jonatso/GuitarZero/mcu/src/crockett.h

#include "mini_midi.h"
#include <stdbool.h>

// Notes
note_t crocetts_theme_note0 = {
  110,
  1,
  50,
  0,
  false
};
note_t crocetts_theme_note1 = {
  117,
  1,
  38,
  0,
  false
};
note_t crocetts_theme_note2 = {
  112,
  1,
  38,
  0,
  false
};
note_t crocetts_theme_note3 = {
  119,
  1,
  50,
  0,
  false
};
note_t crocetts_theme_note4 = {
  110,
  1,
  38,
  0,
  false
};
note_t crocetts_theme_note5 = {
  104,
  1,
  50,
  0,
  false
};
note_t crocetts_theme_note6 = {
  115,
  1,
  38,
  0,
  false
};
note_t crocetts_theme_note7 = {
  107,
  1,
  38,
  0,
  false
};
note_t crocetts_theme_note8 = {
  122,
  1,
  38,
  0,
  false
};
note_t crocetts_theme_note9 = {
  119,
  1,
  38,
  0,
  false
};
note_t crocetts_theme_note10 = {
  108,
  1,
  38,
  0,
  false
};
note_t crocetts_theme_note11 = {
  116,
  1,
  38,
  0,
  false
};
note_t crocetts_theme_note12 = {
  105,
  1,
  50,
  0,
  false
};
note_t crocetts_theme_note13 = {
  103,
  1,
  50,
  0,
  false
};
note_t crocetts_theme_note14 = {
  121,
  1,
  50,
  0,
  false
};
note_t crocetts_theme_note15 = {
  117,
  1,
  50,
  0,
  false
};
note_t crocetts_theme_note16 = {
  105,
  1,
  38,
  0,
  false
};
note_t crocetts_theme_note17 = {
  112,
  1,
  50,
  0,
  false
};
note_t crocetts_theme_note18 = {
  109,
  1,
  50,
  0,
  false
};
note_t crocetts_theme_note19 = {
  116,
  1,
  50,
  0,
  false
};
note_t crocetts_theme_note20 = {
  122,
  1,
  50,
  0,
  false
};
note_t crocetts_theme_note21 = {
  105,
  1,
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
  0,
  72,
  3,
  false
};
note_t crocetts_theme_note468 = {
  101,
  0,
  67,
  3,
  false
};
note_t crocetts_theme_note469 = {
  100,
  0,
  68,
  4,
  false
};
note_t crocetts_theme_note470 = {
  95,
  0,
  69,
  5,
  false
};
note_t crocetts_theme_note471 = {
  95,
  0,
  62,
  3,
  false
};
note_t* crocetts_theme_unique_notes[] = {&crocetts_theme_note0,&crocetts_theme_note1,&crocetts_theme_note2,&crocetts_theme_note3,&crocetts_theme_note4,&crocetts_theme_note5,&crocetts_theme_note6,&crocetts_theme_note7,&crocetts_theme_note8,&crocetts_theme_note9,&crocetts_theme_note10,&crocetts_theme_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
};
sixteenth_t crocetts_theme_sixteenth869 = {
  6,
  (uint16_t[]){162,256,187,183,306,320}
};
sixteenth_t crocetts_theme_sixteenth870 = {
  7,
  (uint16_t[]){93,256,187,183,306,378,467}
};
sixteenth_t crocetts_theme_sixteenth871 = {
  6,
  (uint16_t[]){93,256,187,183,306,378}
};
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
