jonatso/GuitarZero/mcu/src/supermario.h

#include "mini_midi.h"
#include <stdbool.h>

// Notes
note_t super_mario_note0 = {
  67,
  0,
  76,
  2,
  false
};
note_t super_mario_note1 = {
  67,
  0,
  72,
  3,
  false
};
note_t super_mario_note2 = {
  67,
  0,
  79,
  5,
  false
};
note_t super_mario_note3 = {
  67,
  0,
  67,
  3,
  false
};
note_t super_mario_note4 = {
  67,
  0,
  64,
  5,
  false
};
note_t super_mario_note5 = {
  67,
  0,
  69,
  5,
  false
};
note_t super_mario_note6 = {
  67,
  0,
  71,
  2,
  false
};
note_t super_mario_note7 = {
  67,
  0,
  70,
  1,
  false
};
note_t super_mario_note8 = {
  67,
  0,
  81,
  2,
  false
};
note_t super_mario_note9 = {
  67,
  0,
  77,
  3,
  false
};
note_t super_mario_note10 = {
  67,
  0,
  74,
  5,
  false
};
note_t super_mario_note11 = {
  67,
  0,
  78,
  4,
  false
};
note_t super_mario_note12 = {
  67,
  0,
  75,
  1,
  false
};
note_t super_mario_note13 = {
  67,
  0,
  68,
  4,
  false
};
note_t super_mario_note14 = {
  67,
  0,
  84,
  5,
  false
};
note_t super_mario_note15 = {
  67,
  4,
  76,
  0,
  true
};
note_t super_mario_note16 = {
  67,
  4,
  72,
  0,
  true
};
note_t super_mario_note17 = {
  67,
  4,
  79,
  0,
  true
};
note_t super_mario_note18 = {
  67,
  4,
  67,
  0,
  true
};
note_t super_mario_note19 = {
  67,
  4,
  64,
  0,
  true
};
note_t super_mario_note20 = {
  67,
  4,
  69,
  0,
  true
};
note_t super_mario_note21 = {
  67,
  4,
  71,
  0,
  true
};
note_t super_mario_note22 = {
  67,
  4,
  70,
  0,
  true
};
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
th117,&super_mario_sixteenth118};
// Song
uint16_t super_mario_sixteenth_indexes[] = {0,0,1,0,1,2,3,1,4,1,1,1,5,1,1,1,6,1,1,7,1,1,8,1,1,9,1,10,1,11,12,1,13,14,1,15,16,1,17,18,1,19,1,20,21,22,1,1,23,1,1,24,1,1,25,1,1,26,1,22,1,27,26,1,24,28,1,29,30,1,31,32,1,33,1,34,21,22,1,1,35,1,36,37,38,39,40,41,42,43,44,45,40,46,47,48,35,1,49,50,51,52,53,54,1,55,1,55,55,1,53,1,35,1,56,57,58,59,40,60,42,61,62,63,40,64,65,66,35,1,67,1,1,68,1,1,69,1,1,53,53,1,35,1,35,1,56,57,58,59,40,60,42,61,62,63,40,64,65,66,35,1,56,70,58,59,53,71,1,55,1,55,55,1,53,1,35,1,56,57,58,59,40,60,42,61,62,63,40,64,65,66,35,1,67,1,1,68,1,1,69,1,1,53,53,1,35,1,72,73,1,74,1,73,75,1,76,77,1,78,79,1,80,1,72,73,1,74,1,73,75,81,53,1,1,35,1,1,80,1,72,73,1,74,1,73,75,1,76,77,1,78,79,1,80,1,82,82,1,82,1,83,82,1,84,1,1,1,85,1,1,1,86,1,1,87,1,1,88,1,1,89,1,90,1,91,89,1,87,92,1,93,94,1,95,96,1,97,1,98,99,90,1,1,86,1,1,87,1,1,88,1,1,89,1,90,1,91,89,1,87,92,1,93,94,1,95,96,1,97,1,98,99,90,1,1,100,101,1,102,53,1,103,1,104,105,42,105,106,40,42,1,107,108,1,109,110,56,111,93,112,101,53,62,113,40,53,1,100,101,1,102,53,1,103,1,104,105,42,105,106,40,42,1,114,115,1,115,115,116,1,93,63,117,53,117,118,1,1,1,100,101,1,102,53,1,103,1,104,105,42,105,106,40,42,1,107,108,1,109,110,56,111,93,112,101,53,62,113,40,53,1,100,101,1,102,53,1,103,1,104,105,42,105,106,40,42,1,114,115,1,115,115,116,1,93,63,117,53,117,118,1,1,1,72,73,1,74,1,73,75,1,76,77,1,78,79,1,80,1,72,73,1,74,1,73,75,81,53,1,1,35,1,1,80,1,72,73,1,74,1,73,75,1,76,77,1,78,79,1,80,1,82,82,1,82,1,83,82,1,84,1,1,1,85,1,1,1,100,101,1,102,53,1,103,1,104,105,42,105,106,40,42,1,107,108,1,109,110,56,111,93,112,101,53,62,113,40,53,1,100,101,1,102,53,1,103,1,104,105,42,105,106,40,42,1,114,115,1,115,115,116,1,93,63,117,53,117,118,1,1,1};
song_t super_mario_song = {
  "SUPER MARIO",
  90,
  37,
  119,
  66,
  super_mario_sixteenth_indexes,
  super_mario_unique_sixteenths,
  super_mario_unique_notes
};
