jonatso/GuitarZero/mcu/src/bjornen_sover.h

#include "mini_midi.h"
#include <stdbool.h>

// Notes
note_t bjornen_sover_note0 = {
  68,
  2,
  52,
  0,
  false
};
note_t bjornen_sover_note1 = {
  68,
  2,
  48,
  0,
  false
};
note_t bjornen_sover_note2 = {
  68,
  2,
  55,
  0,
  false
};
note_t bjornen_sover_note3 = {
  75,
  2,
  47,
  0,
  false
};
note_t bjornen_sover_note4 = {
  75,
  2,
  50,
  0,
  false
};
note_t bjornen_sover_note5 = {
  75,
  2,
  55,
  0,
  false
};
note_t bjornen_sover_note6 = {
  74,
  2,
  55,
  0,
  false
};
note_t bjornen_sover_note7 = {
  74,
  2,
  52,
  0,
  false
};
note_t bjornen_sover_note8 = {
  74,
  2,
  48,
  0,
  false
};
note_t bjornen_sover_note9 = {
  77,
  2,
  47,
  0,
  false
};
note_t bjornen_sover_note10 = {
  77,
  2,
  50,
  0,
  false
};
note_t bjornen_sover_note11 = {
  77,
  2,
  55,
  0,
  false
};
note_t bjornen_sover_note12 = {
  76,
  2,
  55,
  0,
  false
};
note_t bjornen_sover_note13 = {
  76,
  2,
  52,
  0,
  false
};
note_t bjornen_sover_note14 = {
  76,
  2,
  48,
  0,
  false
};
note_t bjornen_sover_note15 = {
  72,
  2,
  55,
  0,
  false
};
note_t bjornen_sover_note16 = {
  72,
  2,
  52,
  0,
  false
};
note_t bjornen_sover_note17 = {
  72,
  2,
  48,
  0,
  false
};
note_t bjornen_sover_note18 = {
  92,
  2,
  55,
  0,
  false
};
note_t bjornen_sover_note19 = {
  92,
  2,
  50,
  0,
  false
};
note_t bjornen_sover_note20 = {
  92,
  2,
  47,
  0,
  false
};
note_t bjornen_sover_note21 = {
  79,
  2,
  48,
  0,
  false
};
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
  5,
  (uint16_t[]){11,9,10,45,73}
};
sixteenth_t bjornen_sover_sixteenth71 = {
  4,
  (uint16_t[]){11,9,10,45}
};
sixteenth_t bjornen_sover_sixteenth72 = {
  5,
  (uint16_t[]){15,16,17,24,73}
};
sixteenth_t bjornen_sover_sixteenth73 = {
  4,
  (uint16_t[]){15,16,17,24}
};
sixteenth_t* bjornen_sover_unique_sixteenths[] = {&bjornen_sover_sixteenth0,&bjornen_sover_sixteenth1,&bjornen_sover_sixteenth2,&bjornen_sover_sixteenth3,&bjornen_sover_sixteenth4,&bjornen_sover_sixteenth5,&bjornen_sover_sixteenth6,&bjornen_sover_sixteenth7,&bjornen_sover_sixteenth8,&bjornen_sover_sixteenth9,&bjornen_sover_sixteenth10,&bjornen_sover_sixteenth11,&bjornen_sover_sixteenth12,&bjornen_sover_sixteenth13,&bjornen_sover_sixteenth14,&bjornen_sover_sixteenth15,&bjornen_sover_sixteenth16,&bjornen_sover_sixteenth17,&bjornen_sover_sixteenth18,&bjornen_sover_sixteenth19,&bjornen_sover_sixteenth20,&bjornen_sover_sixteenth21,&bjornen_sover_sixteenth22,&bjornen_sover_sixteenth23,&bjornen_sover_sixteenth24,&bjornen_sover_sixteenth25,&bjornen_sover_sixteenth26,&bjornen_sover_sixteenth27,&bjornen_sover_sixteenth28,&bjornen_sover_sixteenth29,&bjornen_sover_sixteenth30,&bjornen_sover_sixteenth31,&bjornen_sover_sixteenth32,&bjornen_sover_sixteenth33,&bjornen_sover_sixteenth34,&bjornen_sover_sixteenth35,&bjornen_sover_sixteenth36,&bjornen_sover_sixteenth37,&bjornen_sover_sixteenth38,&bjornen_sover_sixteenth39,&bjornen_sover_sixteenth40,&bjornen_sover_sixteenth41,&bjornen_sover_sixteenth42,&bjornen_sover_sixteenth43,&bjornen_sover_sixteenth44,&bjornen_sover_sixteenth45,&bjornen_sover_sixteenth46,&bjornen_sover_sixteenth47,&bjornen_sover_sixteenth48,&bjornen_sover_sixteenth49,&bjornen_sover_sixteenth50,&bjornen_sover_sixteenth51,&bjornen_sover_sixteenth52,&bjornen_sover_sixteenth53,&bjornen_sover_sixteenth54,&bjornen_sover_sixteenth55,&bjornen_sover_sixteenth56,&bjornen_sover_sixteenth57,&bjornen_sover_sixteenth58,&bjornen_sover_sixteenth59,&bjornen_sover_sixteenth60,&bjornen_sover_sixteenth61,&bjornen_sover_sixteenth62,&bjornen_sover_sixteenth63,&bjornen_sover_sixteenth64,&bjornen_sover_sixteenth65,&bjornen_sover_sixteenth66,&bjornen_sover_sixteenth67,&bjornen_sover_sixteenth68,&bjornen_sover_sixteenth69,&bjornen_sover_sixteenth70,&bjornen_sover_sixteenth71,&bjornen_sover_sixteenth72,&bjornen_sover_sixteenth73};
// Song
uint16_t bjornen_sover_sixteenth_indexes[] = {0,1,1,1,2,3,3,3,4,5,5,5,6,7,7,7,8,9,9,9,10,11,11,11,12,13,13,13,14,15,15,15,16,17,17,17,16,17,17,17,18,19,19,19,20,21,21,21,22,23,23,23,23,23,23,23,23,23,23,23,23,23,23,23,24,25,25,25,26,27,27,27,28,29,29,29,30,31,31,31,32,33,33,33,33,33,33,33,34,35,35,35,35,35,35,35,36,37,37,37,38,39,39,39,40,41,41,41,42,43,43,43,44,45,45,45,45,45,45,45,46,47,47,47,47,47,47,47,48,49,49,49,50,51,51,51,52,53,53,53,54,55,55,55,56,57,57,57,58,59,59,59,60,61,61,61,62,63,63,63,64,65,65,65,66,67,67,67,68,69,69,69,70,71,71,71,72,73,73,73,73,73,73,73,73,73,73,73,73,73,73,73};
song_t bjornen_sover_song = {
  "BJORNEN SOVER",
  100,
  12,
  74,
  74,
  bjornen_sover_sixteenth_indexes,
  bjornen_sover_unique_sixteenths,
  bjornen_sover_unique_notes
};
