jonatso/GuitarZero/mcu/src/eye_of_the_tiger.h

#include "mini_midi.h"
#include <stdbool.h>

// Notes
note_t eye_of_the_tiger_note0 = {
  117,
  4,
  65,
  0,
  true
};
note_t eye_of_the_tiger_note1 = {
  117,
  4,
  77,
  0,
  true
};
note_t eye_of_the_tiger_note2 = {
  112,
  4,
  68,
  0,
  true
};
note_t eye_of_the_tiger_note3 = {
  112,
  4,
  80,
  0,
  true
};
note_t eye_of_the_tiger_note4 = {
  114,
  4,
  65,
  0,
  true
};
note_t eye_of_the_tiger_note5 = {
  114,
  4,
  77,
  0,
  true
};
note_t eye_of_the_tiger_note6 = {
  121,
  4,
  63,
  0,
  true
};
note_t eye_of_the_tiger_note7 = {
  121,
  4,
  75,
  0,
  true
};
note_t eye_of_the_tiger_note8 = {
  94,
  4,
  61,
  0,
  true
};
note_t eye_of_the_tiger_note9 = {
  94,
  4,
  73,
  0,
  true
};
note_t eye_of_the_tiger_note10 = {
  96,
  4,
  65,
  0,
  true
};
note_t eye_of_the_tiger_note11 = {
  96,
  4,
  77,
  0,
  true
};
note_t eye_of_the_tiger_note12 = {
  95,
  4,
  75,
  0,
  true
};
note_t eye_of_the_tiger_note13 = {
  95,
  4,
  63,
  0,
  true
};
note_t eye_of_the_tiger_note14 = {
  101,
  4,
  73,
  0,
  true
};
note_t eye_of_the_tiger_note15 = {
  101,
  4,
  61,
  0,
  true
};
note_t eye_of_the_tiger_note16 = {
  91,
  4,
  73,
  0,
  true
};
note_t eye_of_the_tiger_note17 = {
  91,
  4,
  61,
  0,
  true
};
note_t eye_of_the_tiger_note18 = {
  94,
  4,
  63,
  0,
  true
};
note_t eye_of_the_tiger_note19 = {
  94,
  4,
  75,
  0,
  true
};
note_t eye_of_the_tiger_note20 = {
  93,
  4,
  75,
  0,
  true
};
note_t eye_of_the_tiger_note21 = {
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
e_of_the_tiger_note464,&eye_of_the_tiger_note465,&eye_of_the_tiger_note466,&eye_of_the_tiger_note467,&eye_of_the_tiger_note468,&eye_of_the_tiger_note469,&eye_of_the_tiger_note470,&eye_of_the_tiger_note471,&eye_of_the_tiger_note472,&eye_of_the_tiger_note473,&eye_of_the_tiger_note474,&eye_of_the_tiger_note475,&eye_of_the_tiger_note476,&eye_of_the_tiger_note477,&eye_of_the_tiger_note478,&eye_of_the_tiger_note479,&eye_of_the_tiger_note480,&eye_of_the_tiger_note481,&eye_of_the_tiger_note482,&eye_of_the_tiger_note483,&eye_of_the_tiger_note484,&eye_of_the_tiger_note485,&eye_of_the_tiger_note486,&eye_of_the_tiger_note487,&eye_of_the_tiger_note488,&eye_of_the_tiger_note489,&eye_of_the_tiger_note490,&eye_of_the_tiger_note491,&eye_of_the_tiger_note492,&eye_of_the_tiger_note493,&eye_of_the_tiger_note494,&eye_of_the_tiger_note495,&eye_of_the_tiger_note496,&eye_of_the_tiger_note497,&eye_of_the_tiger_note498,&eye_of_the_tiger_note499,&eye_of_the_tiger_note500,&eye_of_the_tiger_note501,&eye_of_the_tiger_note502,&eye_of_the_tiger_note503,&eye_of_the_tiger_note504,&eye_of_the_tiger_note505,&eye_of_the_tiger_note506,&eye_of_the_tiger_note507,&eye_of_the_tiger_note508,&eye_of_the_tiger_note509,&eye_of_the_tiger_note510,&eye_of_the_tiger_note511,&eye_of_the_tiger_note512,&eye_of_the_tiger_note513,&eye_of_the_tiger_note514,&eye_of_the_tiger_note515,&eye_of_the_tiger_note516,&eye_of_the_tiger_note517,&eye_of_the_tiger_note518,&eye_of_the_tiger_note519,&eye_of_the_tiger_note520,&eye_of_the_tiger_note521,&eye_of_the_tiger_note522,&eye_of_the_tiger_note523,&eye_of_the_tiger_note524,&eye_of_the_tiger_note525,&eye_of_the_tiger_note526,&eye_of_the_tiger_note527,&eye_of_the_tiger_note528,&eye_of_the_tiger_note529,&eye_of_the_tiger_note530,&eye_of_the_tiger_note531,&eye_of_the_tiger_note532,&eye_of_the_tiger_note533,&eye_of_the_tiger_note534,&eye_of_the_tiger_note535,&eye_of_the_tiger_note536,&eye_of_the_tiger_note537,&eye_of_the_tiger_note538,&eye_of_the_tiger_note539,&eye_of_the_tiger_note540,&eye_of_the_tiger_note541,&eye_of_the_tiger_note542,&eye_of_the_tiger_note543,&eye_of_the_tiger_note544,&eye_of_the_tiger_note545,&eye_of_the_tiger_note546,&eye_of_the_tiger_note547,&eye_of_the_tiger_note548,&eye_of_the_tiger_note549,&eye_of_the_tiger_note550,&eye_of_the_tiger_note551,&eye_of_the_tiger_note552,&eye_of_the_tiger_note553,&eye_of_the_tiger_note554};
// Sixteenths
sixteenth_t eye_of_the_tiger_sixteenth0 = {
  0,
  (uint16_t[]){}
};
sixteenth_t eye_of_the_tiger_sixteenth1 = {
  8,
  (uint16_t[]){261,278,279,305,307,306,412,411}
};
sixteenth_t eye_of_the_tiger_sixteenth2 = {
  4,
  (uint16_t[]){261,306,412,411}
};
sixteenth_t eye_of_the_tiger_sixteenth3 = {
  8,
  (uint16_t[]){261,279,279,305,309,308,414,413}
};
sixteenth_t eye_of_the_tiger_sixteenth4 = {
  3,
  (uint16_t[]){261,414,413}
};
sixteenth_t eye_of_the_tiger_sixteenth5 = {
  8,
  (uint16_t[]){262,280,281,311,312,310,415,416}
};
sixteenth_t eye_of_the_tiger_sixteenth6 = {
  2,
  (uint16_t[]){262,416}
};
sixteenth_t eye_of_the_tiger_sixteenth7 = {
  8,
  (uint16_t[]){261,281,281,314,313,315,413,417}
};
sixteenth_t eye_of_the_tiger_sixteenth8 = {
  3,
  (uint16_t[]){261,413,417}
};
sixteenth_t eye_of_the_tiger_sixteenth9 = {
  2,
  (uint16_t[]){413,417}
};
sixteenth_t eye_of_the_tiger_sixteenth10 = {
  8,
  (uint16_t[]){261,281,281,317,308,316,419,418}
};
sixteenth_t eye_of_the_tiger_sixteenth11 = {
  3,
  (uint16_t[]){261,419,418}
};
sixteenth_t eye_of_the_tiger_sixteenth12 = {
  8,
  (uint16_t[]){262,281,281,318,319,312,420,416}
};
sixteenth_t eye_of_the_tiger_sixteenth13 = {
  1,
  (uint16_t[]){262}
};
sixteenth_t eye_of_the_tiger_sixteenth14 = {
  8,
  (uint16_t[]){261,281,281,306,320,305,414,412}
};
sixteenth_t eye_of_the_tiger_sixteenth15 = {
  3,
  (uint16_t[]){261,414,412}
};
sixteenth_t eye_of_the_tiger_sixteenth16 = {
  2,
  (uint16_t[]){414,412}
};
sixteenth_t eye_of_the_tiger_sixteenth17 = {
  8,
  (uint16_t[]){261,281,281,321,316,322,421,412}
};
sixteenth_t eye_of_the_tiger_sixteenth18 = {
  6,
  (uint16_t[]){261,321,316,322,421,412}
};
sixteenth_t eye_of_the_tiger_sixteenth19 = {
  7,
  (uint16_t[]){263,282,283,323,324,422,423}
};
sixteenth_t eye_of_the_tiger_sixteenth20 = {
  3,
  (uint16_t[]){263,422,423}
};
sixteenth_t eye_of_the_tiger_sixteenth21 = {
  8,
  (uint16_t[]){264,284,285,326,308,325,424,425}
};
sixteenth_t eye_of_the_tiger_sixteenth22 = {
  6,
  (uint16_t[]){264,326,308,325,424,425}
};
sixteenth_t eye_of_the_tiger_sixteenth23 = {
  4,
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
};
sixteenth_t eye_of_the_tiger_sixteenth735 = {
  9,
  (uint16_t[]){12,13,254,265,373,380,341,458,472}
};
sixteenth_t eye_of_the_tiger_sixteenth736 = {
  6,
  (uint16_t[]){12,13,265,373,380,341}
};
sixteenth_t eye_of_the_tiger_sixteenth737 = {
  5,
  (uint16_t[]){17,16,265,524,525}
};
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
