jonatso/GuitarZero/mcu/src/kickstart_my_heart.h

#include "mini_midi.h"
#include <stdbool.h>

// Notes
note_t kickstart_my_heart_note0 = {
  95,
  3,
  48,
  0,
  false
};
note_t kickstart_my_heart_note1 = {
  95,
  3,
  53,
  0,
  false
};
note_t kickstart_my_heart_note2 = {
  95,
  3,
  41,
  0,
  false
};
note_t kickstart_my_heart_note3 = {
  95,
  3,
  54,
  0,
  false
};
note_t kickstart_my_heart_note4 = {
  95,
  3,
  49,
  0,
  false
};
note_t kickstart_my_heart_note5 = {
  95,
  3,
  42,
  0,
  false
};
note_t kickstart_my_heart_note6 = {
  95,
  3,
  55,
  0,
  false
};
note_t kickstart_my_heart_note7 = {
  95,
  3,
  50,
  0,
  false
};
note_t kickstart_my_heart_note8 = {
  95,
  3,
  43,
  0,
  false
};
note_t kickstart_my_heart_note9 = {
  95,
  3,
  46,
  0,
  false
};
note_t kickstart_my_heart_note10 = {
  70,
  3,
  43,
  0,
  false
};
note_t kickstart_my_heart_note11 = {
  95,
  3,
  45,
  0,
  false
};
note_t kickstart_my_heart_note12 = {
  95,
  3,
  47,
  0,
  false
};
note_t kickstart_my_heart_note13 = {
  95,
  3,
  64,
  0,
  false
};
note_t kickstart_my_heart_note14 = {
  95,
  3,
  60,
  0,
  false
};
note_t kickstart_my_heart_note15 = {
  95,
  3,
  65,
  0,
  false
};
note_t kickstart_my_heart_note16 = {
  70,
  3,
  64,
  0,
  false
};
note_t kickstart_my_heart_note17 = {
  95,
  3,
  38,
  0,
  false
};
note_t kickstart_my_heart_note18 = {
  95,
  3,
  40,
  0,
  false
};
note_t kickstart_my_heart_note19 = {
  95,
  3,
  58,
  0,
  false
};
note_t kickstart_my_heart_note20 = {
  95,
  3,
  39,
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
  1,
  false
};
note_t kickstart_my_heart_note81 = {
  95,
  0,
  38,
  4,
  false
};
note_t kickstart_my_heart_note82 = {
  95,
  0,
  40,
  1,
  false
};
note_t kickstart_my_heart_note83 = {
  95,
  0,
  39,
  5,
  false
};
note_t kickstart_my_heart_note84 = {
  63,
  0,
  60,
  1,
  false
};
note_t kickstart_my_heart_note85 = {
  63,
  0,
  65,
  1,
  false
};
note_t kickstart_my_heart_note86 = {
  63,
  0,
  48,
  4,
  false
};
note_t kickstart_my_heart_note87 = {
  63,
  0,
  55,
  1,
  false
};
note_t kickstart_my_heart_note88 = {
  37,
  0,
  64,
  5,
  false
};
note_t kickstart_my_heart_note89 = {
  63,
  0,
  64,
  5,
  false
};
note_t kickstart_my_heart_note90 = {
  95,
  0,
  59,
  5,
  false
};
note_t kickstart_my_heart_note91 = {
  70,
  0,
  46,
  2,
  false
};
note_t kickstart_my_heart_note92 = {
  70,
  0,
  47,
  3,
  false
};
note_t kickstart_my_heart_note93 = {
  95,
  0,
  54,
  5,
  false
};
note_t kickstart_my_heart_note94 = {
  95,
  0,
  52,
  3,
  false
};
note_t kickstart_my_heart_note95 = {
  95,
  0,
  57,
  3,
  false
};
note_t* kickstart_my_heart_unique_notes[] = {&kickstart_my_heart_note0,&kickstart_my_heart_note1,&kickstart_my_heart_note2,&kickstart_my_heart_note3,&kickstart_my_heart_note4,&kickstart_my_heart_note5,&kickstart_my_heart_note6,&kickstart_my_heart_note7,&kickstart_my_heart_note8,&kickstart_my_heart_note9,&kickstart_my_heart_note10,&kickstart_my_heart_note11,&kickstart_my_heart_note12,&kickstart_my_heart_note13,&kickstart_my_heart_note14,&kickstart_my_heart_note15,&kickstart_my_heart_note16,&kickstart_my_heart_note17,&kickstart_my_heart_note18,&kickstart_my_heart_note19,&kickstart_my_heart_note20,&kickstart_my_heart_note21,&kickstart_my_heart_note22,&kickstart_my_heart_note23,&kickstart_my_heart_note24,&kickstart_my_heart_note25,&kickstart_my_heart_note26,&kickstart_my_heart_note27,&kickstart_my_heart_note28,&kickstart_my_heart_note29,&kickstart_my_heart_note30,&kickstart_my_heart_note31,&kickstart_my_heart_note32,&kickstart_my_heart_note33,&kickstart_my_heart_note34,&kickstart_my_heart_note35,&kickstart_my_heart_note36,&kickstart_my_heart_note37,&kickstart_my_heart_note38,&kickstart_my_heart_note39,&kickstart_my_heart_note40,&kickstart_my_heart_note41,&kickstart_my_heart_note42,&kickstart_my_heart_note43,&kickstart_my_heart_note44,&kickstart_my_heart_note45,&kickstart_my_heart_note46,&kickstart_my_heart_note47,&kickstart_my_heart_note48,&kickstart_my_heart_note49,&kickstart_my_heart_note50,&kickstart_my_heart_note51,&kickstart_my_heart_note52,&kickstart_my_heart_note53,&kickstart_my_heart_note54,&kickstart_my_heart_note55,&kickstart_my_heart_note56,&kickstart_my_heart_note57,&kickstart_my_heart_note58,&kickstart_my_heart_note59,&kickstart_my_heart_note60,&kickstart_my_heart_note61,&kickstart_my_heart_note62,&kickstart_my_heart_note63,&kickstart_my_heart_note64,&kickstart_my_heart_note65,&kickstart_my_heart_note66,&kickstart_my_heart_note67,&kickstart_my_heart_note68,&kickstart_my_heart_note69,&kickstart_my_heart_note70,&kickstart_my_heart_note71,&kickstart_my_heart_note72,&kickstart_my_heart_note73,&kickstart_my_heart_note74,&kickstart_my_heart_note75,&kickstart_my_heart_note76,&kickstart_my_heart_note77,&kickstart_my_heart_note78,&kickstart_my_heart_note79,&kickstart_my_heart_note80,&kickstart_my_heart_note81,&kickstart_my_heart_note82,&kickstart_my_heart_note83,&kickstart_my_heart_note84,&kickstart_my_heart_note85,&kickstart_my_heart_note86,&kickstart_my_heart_note87,&kickstart_my_heart_note88,&kickstart_my_heart_note89,&kickstart_my_heart_note90,&kickstart_my_heart_note91,&kickstart_my_heart_note92,&kickstart_my_heart_note93,&kickstart_my_heart_note94,&kickstart_my_heart_note95};
// Sixteenths
sixteenth_t kickstart_my_heart_sixteenth0 = {
  0,
  (uint16_t[]){}
};
sixteenth_t kickstart_my_heart_sixteenth1 = {
  3,
  (uint16_t[]){0,2,1}
};
sixteenth_t kickstart_my_heart_sixteenth2 = {
  3,
  (uint16_t[]){5,4,3}
};
sixteenth_t kickstart_my_heart_sixteenth3 = {
  3,
  (uint16_t[]){8,6,7}
};
sixteenth_t kickstart_my_heart_sixteenth4 = {
  3,
  (uint16_t[]){6,8,7}
};
sixteenth_t kickstart_my_heart_sixteenth5 = {
  1,
  (uint16_t[]){8}
};
sixteenth_t kickstart_my_heart_sixteenth6 = {
  3,
  (uint16_t[]){6,7,8}
};
sixteenth_t kickstart_my_heart_sixteenth7 = {
  3,
  (uint16_t[]){8,7,6}
};
sixteenth_t kickstart_my_heart_sixteenth8 = {
  3,
  (uint16_t[]){2,1,0}
};
sixteenth_t kickstart_my_heart_sixteenth9 = {
  3,
  (uint16_t[]){5,3,4}
};
sixteenth_t kickstart_my_heart_sixteenth10 = {
  3,
  (uint16_t[]){7,6,8}
};
sixteenth_t kickstart_my_heart_sixteenth11 = {
  3,
  (uint16_t[]){7,8,6}
};
sixteenth_t kickstart_my_heart_sixteenth12 = {
  8,
  (uint16_t[]){1,0,2,27,0,2,1,63}
};
sixteenth_t kickstart_my_heart_sixteenth13 = {
  7,
  (uint16_t[]){1,0,2,27,0,2,1}
};
sixteenth_t kickstart_my_heart_sixteenth14 = {
  7,
  (uint16_t[]){5,3,4,28,5,4,3}
};
sixteenth_t kickstart_my_heart_sixteenth15 = {
  8,
  (uint16_t[]){6,7,8,29,8,6,7,64}
};
sixteenth_t kickstart_my_heart_sixteenth16 = {
  7,
  (uint16_t[]){6,7,8,29,8,6,7}
};
sixteenth_t kickstart_my_heart_sixteenth17 = {
  8,
  (uint16_t[]){8,7,6,29,7,8,6,64}
};
sixteenth_t kickstart_my_heart_sixteenth18 = {
  7,
  (uint16_t[]){8,7,6,29,7,8,6}
};
sixteenth_t kickstart_my_heart_sixteenth19 = {
  3,
  (uint16_t[]){8,29,8}
};
sixteenth_t kickstart_my_heart_sixteenth20 = {
  8,
  (uint16_t[]){6,7,8,29,8,7,6,64}
};
sixteenth_t kickstart_my_heart_sixteenth21 = {
  7,
  (uint16_t[]){6,7,8,29,8,7,6}
};
sixteenth_t kickstart_my_heart_sixteenth22 = {
  8,
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
};
sixteenth_t kickstart_my_heart_sixteenth789 = {
  7,
  (uint16_t[]){6,0,33,6,0,95,95}
};
sixteenth_t kickstart_my_heart_sixteenth790 = {
  12,
  (uint16_t[]){6,0,14,33,6,0,14,95,95,95,95,95}
};
sixteenth_t kickstart_my_heart_sixteenth791 = {
  10,
  (uint16_t[]){6,7,8,29,6,7,8,95,95,95}
};
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
