jonatso/GuitarZero/mcu/src/megalovania.h

#include "mini_midi.h"
#include <stdbool.h>

// Notes
note_t megalovania_note0 = {
  100,
  4,
  62,
  0,
  true
};
note_t megalovania_note1 = {
  100,
  4,
  74,
  0,
  true
};
note_t megalovania_note2 = {
  100,
  4,
  69,
  0,
  true
};
note_t megalovania_note3 = {
  100,
  4,
  68,
  0,
  true
};
note_t megalovania_note4 = {
  100,
  4,
  67,
  0,
  true
};
note_t megalovania_note5 = {
  100,
  4,
  65,
  0,
  true
};
note_t megalovania_note6 = {
  100,
  4,
  60,
  0,
  true
};
note_t megalovania_note7 = {
  100,
  4,
  59,
  0,
  true
};
note_t megalovania_note8 = {
  100,
  4,
  58,
  0,
  true
};
note_t megalovania_note9 = {
  100,
  4,
  72,
  0,
  true
};
note_t megalovania_note10 = {
  100,
  4,
  64,
  0,
  true
};
note_t megalovania_note11 = {
  100,
  4,
  73,
  0,
  true
};
note_t megalovania_note12 = {
  100,
  4,
  53,
  0,
  true
};
note_t megalovania_note13 = {
  100,
  4,
  55,
  0,
  true
};
note_t megalovania_note14 = {
  100,
  4,
  57,
  0,
  true
};
note_t megalovania_note15 = {
  100,
  4,
  61,
  0,
  true
};
note_t megalovania_note16 = {
  100,
  4,
  63,
  0,
  true
};
note_t megalovania_note17 = {
  100,
  4,
  77,
  0,
  true
};
note_t megalovania_note18 = {
  100,
  4,
  76,
  0,
  true
};
note_t megalovania_note19 = {
  100,
  4,
  52,
  0,
  true
};
note_t megalovania_note20 = {
  100,
  4,
  48,
  0,
  true
};
note_t megalovania_note21 = {
  100,
  4,
  50,
  0,
  true
};
note_t megalovania_note22 = {
  100,
  4,
  45,
  0,
  true
};
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
  5,
  (uint16_t[]){7,45,52,50,71}
};
sixteenth_t megalovania_sixteenth55 = {
  5,
  (uint16_t[]){1,28,50,70,71}
};
sixteenth_t megalovania_sixteenth56 = {
  1,
  (uint16_t[]){71}
};
sixteenth_t megalovania_sixteenth57 = {
  5,
  (uint16_t[]){2,28,48,70,71}
};
sixteenth_t megalovania_sixteenth58 = {
  2,
  (uint16_t[]){70,71}
};
sixteenth_t megalovania_sixteenth59 = {
  5,
  (uint16_t[]){3,28,47,70,71}
};
sixteenth_t megalovania_sixteenth60 = {
  5,
  (uint16_t[]){4,28,46,70,71}
};
sixteenth_t megalovania_sixteenth61 = {
  5,
  (uint16_t[]){5,28,43,70,71}
};
sixteenth_t megalovania_sixteenth62 = {
  4,
  (uint16_t[]){5,43,70,71}
};
sixteenth_t megalovania_sixteenth63 = {
  4,
  (uint16_t[]){0,45,70,71}
};
sixteenth_t megalovania_sixteenth64 = {
  4,
  (uint16_t[]){4,46,70,71}
};
sixteenth_t megalovania_sixteenth65 = {
  7,
  (uint16_t[]){8,28,50,45,51,73,72}
};
sixteenth_t megalovania_sixteenth66 = {
  5,
  (uint16_t[]){8,51,50,45,72}
};
sixteenth_t megalovania_sixteenth67 = {
  5,
  (uint16_t[]){1,28,50,73,72}
};
sixteenth_t megalovania_sixteenth68 = {
  1,
  (uint16_t[]){72}
};
sixteenth_t megalovania_sixteenth69 = {
  5,
  (uint16_t[]){2,28,48,73,72}
};
sixteenth_t megalovania_sixteenth70 = {
  2,
  (uint16_t[]){73,72}
};
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
